FPGAwars/icezum/src-kicad/icezum-alhambra-drawing-1.png

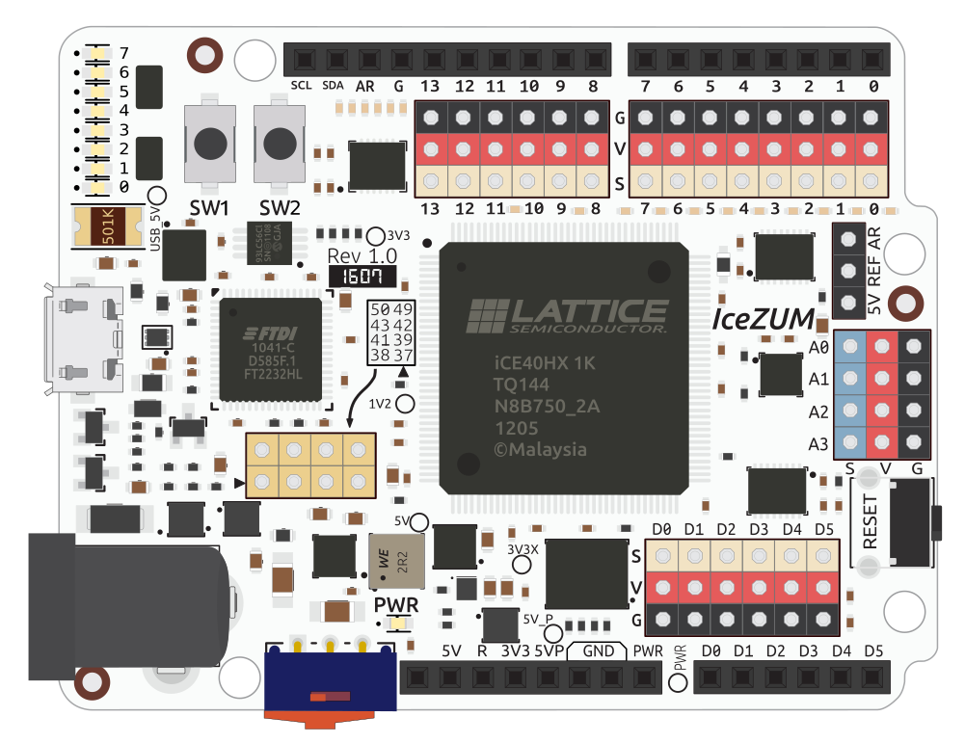
src-kicad/icezum-alhambra-drawing-1.png
