FPGAwars/icezum/src-kicad/images/icezum-block-diagram.png

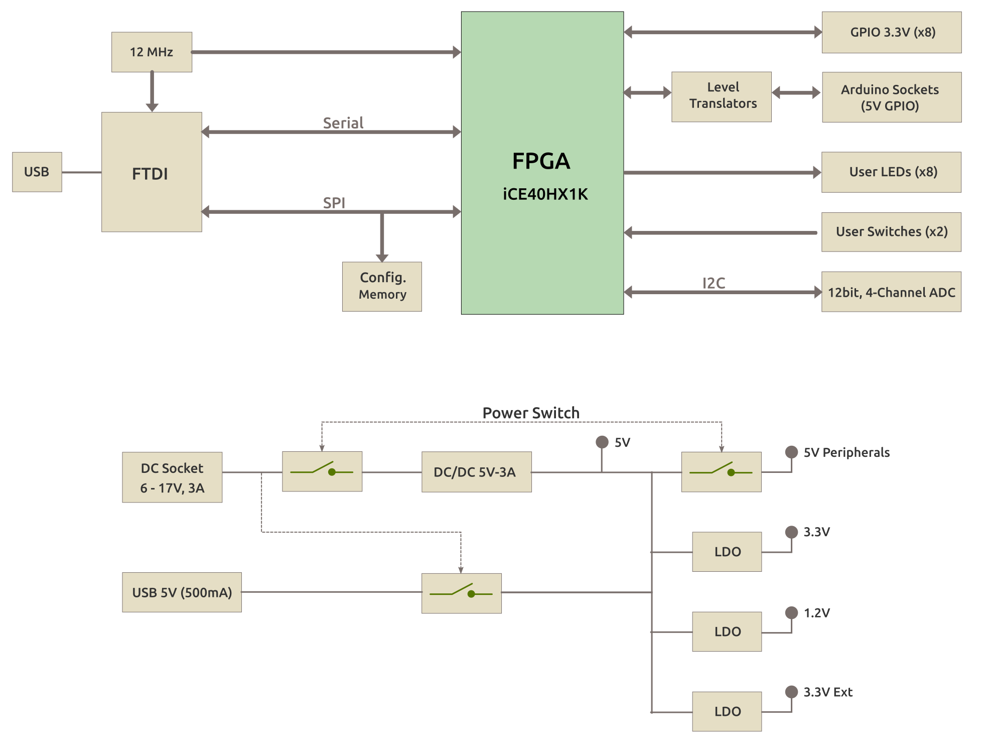
src-kicad/images/icezum-block-diagram.png
