FPGAwars/icezum/wiki/2016-03-04-Mounting-first-prototype/icezum-alhambra-mounting-16.png

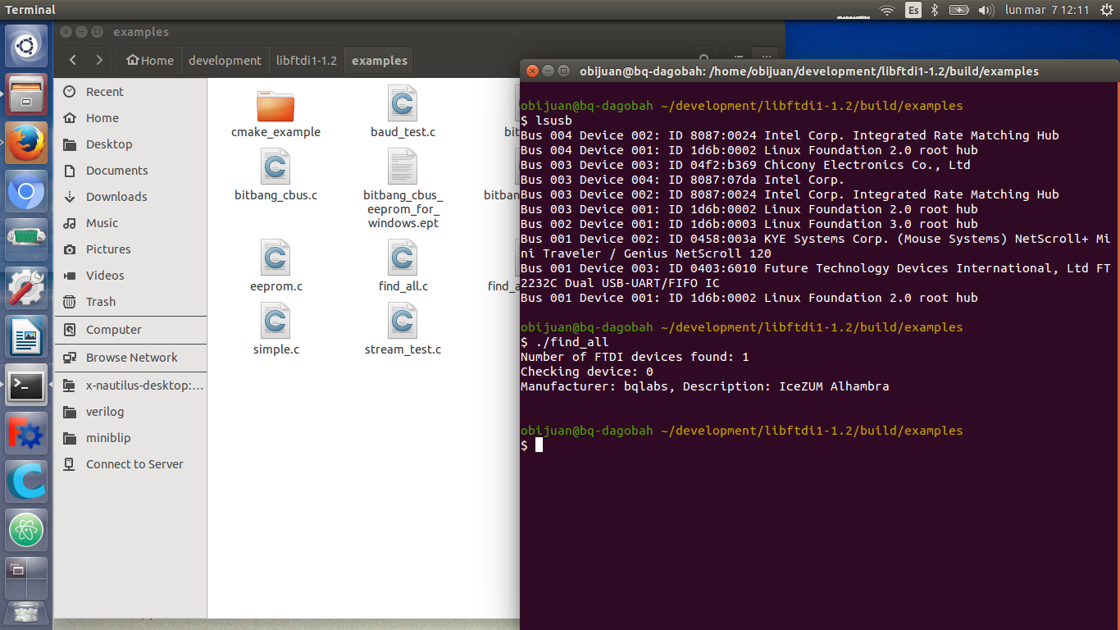
wiki/2016-03-04-Mounting-first-prototype/icezum-alhambra-mounting-16.png
