FPGAwars/icezum/wiki/2016-03-04-Mounting-first-prototype/icezum-alhambra-mounting-18.jpg

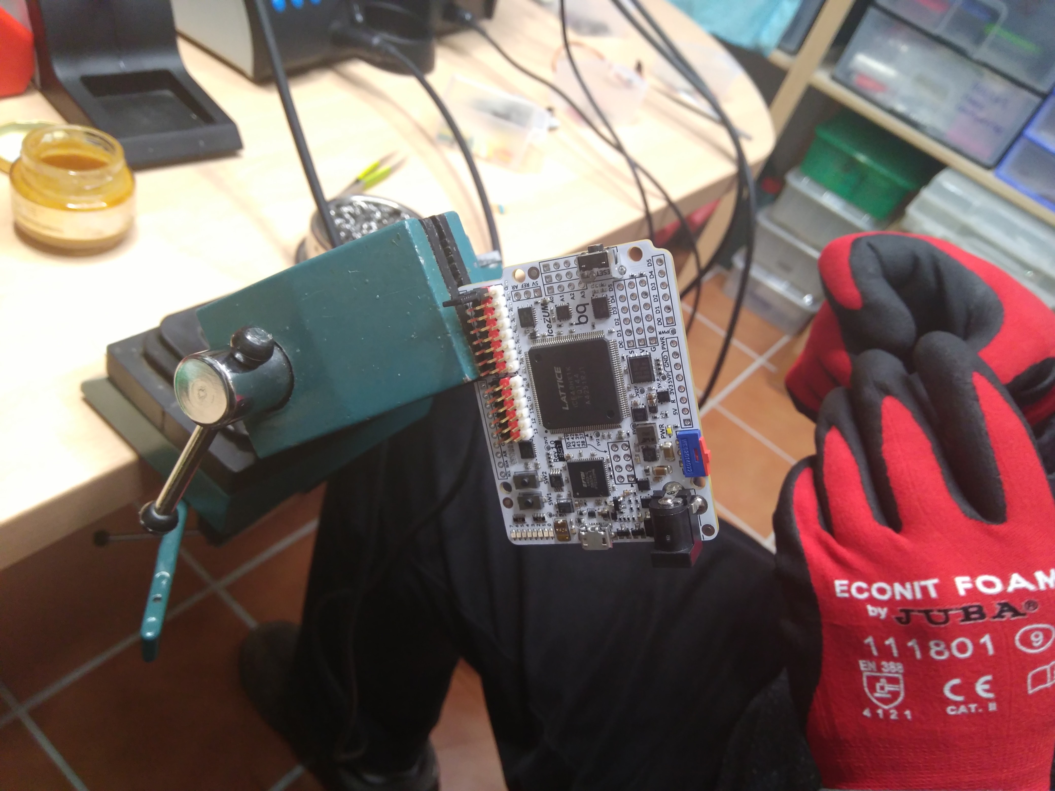
wiki/2016-03-04-Mounting-first-prototype/icezum-alhambra-mounting-18.jpg
