FPGAwars/icezum/wiki/Alhambra_in_the_evening-wikipedia-public-domain.jpg

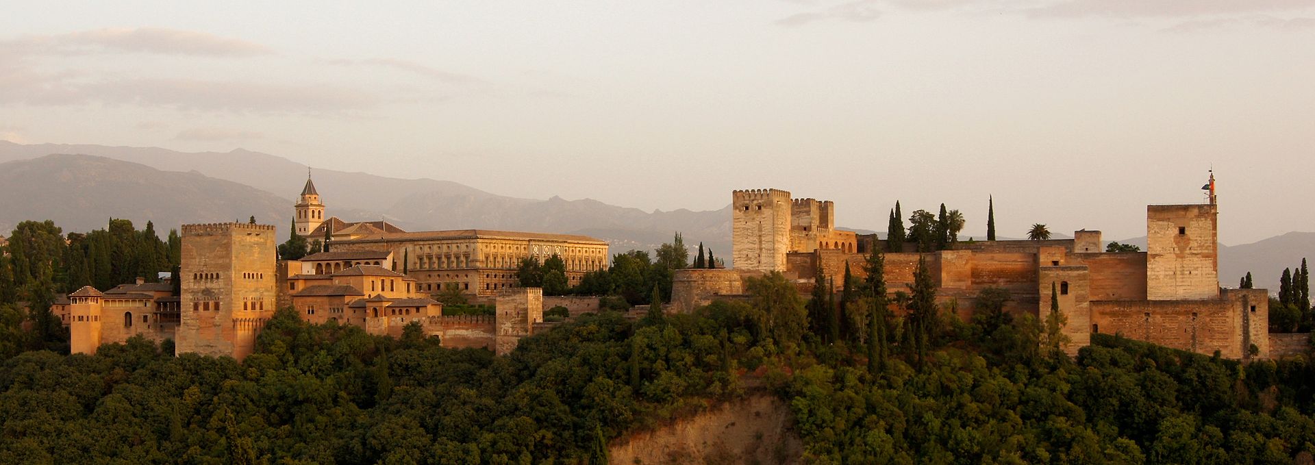
wiki/Alhambra_in_the_evening-wikipedia-public-domain.jpg
