FPGAwars/icezum/wiki/AlhambraFestivales-curdiales.png

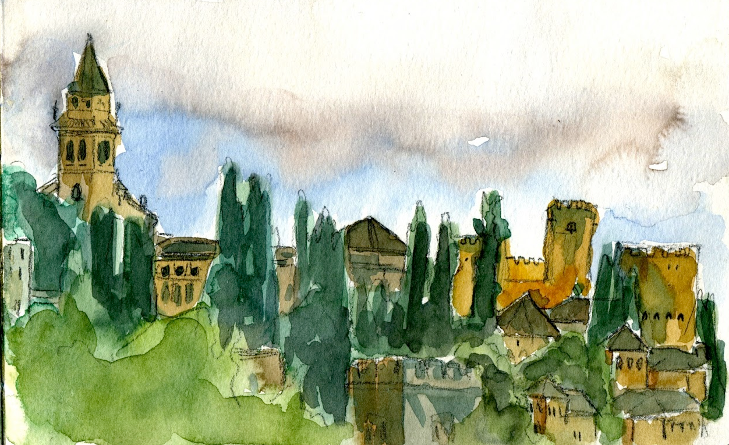
wiki/AlhambraFestivales-curdiales.png
