FPGAwars/icezum/wiki/Icezum-Alhambra-pcb-1.jpg

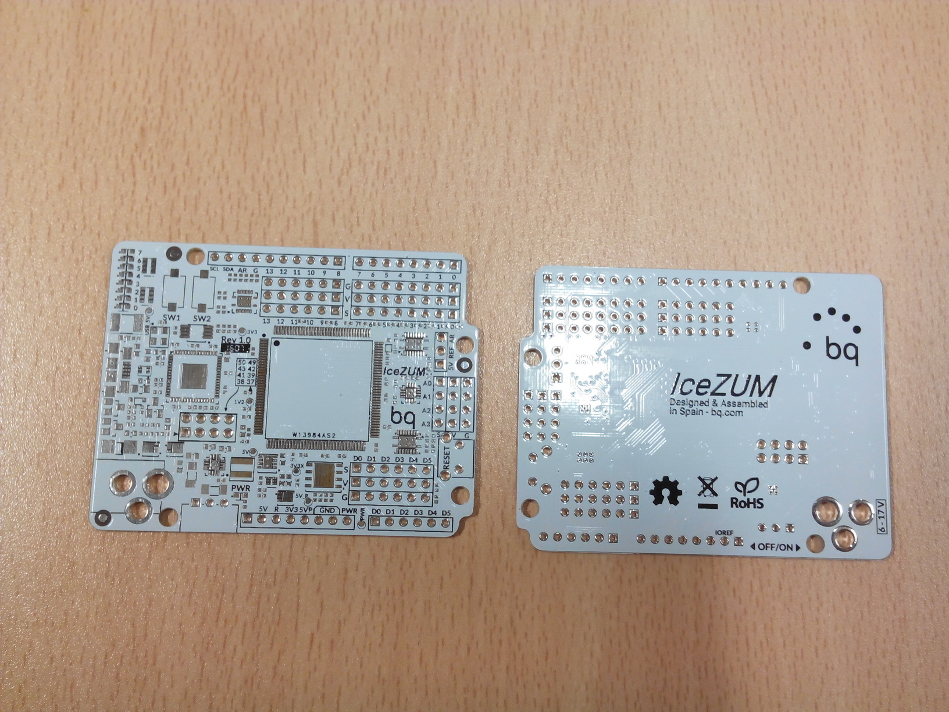
wiki/Icezum-Alhambra-pcb-1.jpg
