FPGAwars/icezum/wiki/icezum-pinout-screenshot-inkscape.png

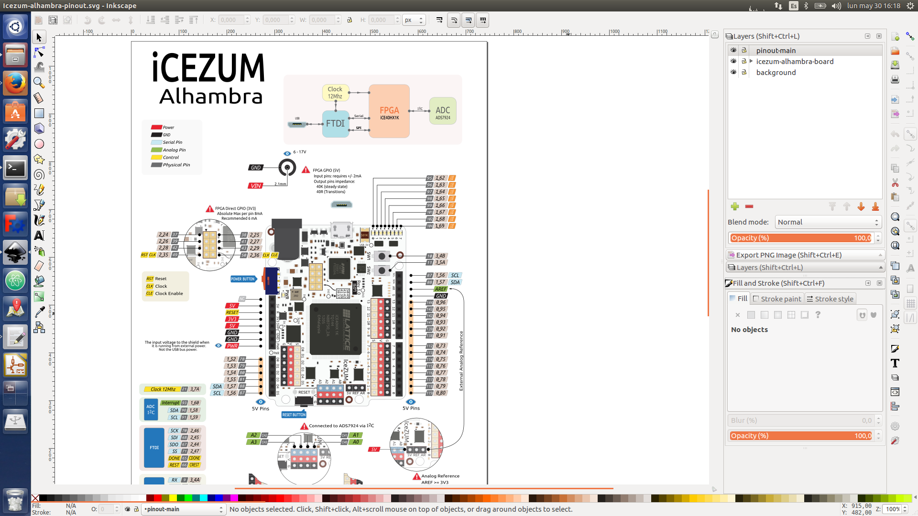
wiki/icezum-pinout-screenshot-inkscape.png
