FPGAwars/icezum/wiki/Icezum-rev1-1607-img1-peq.png

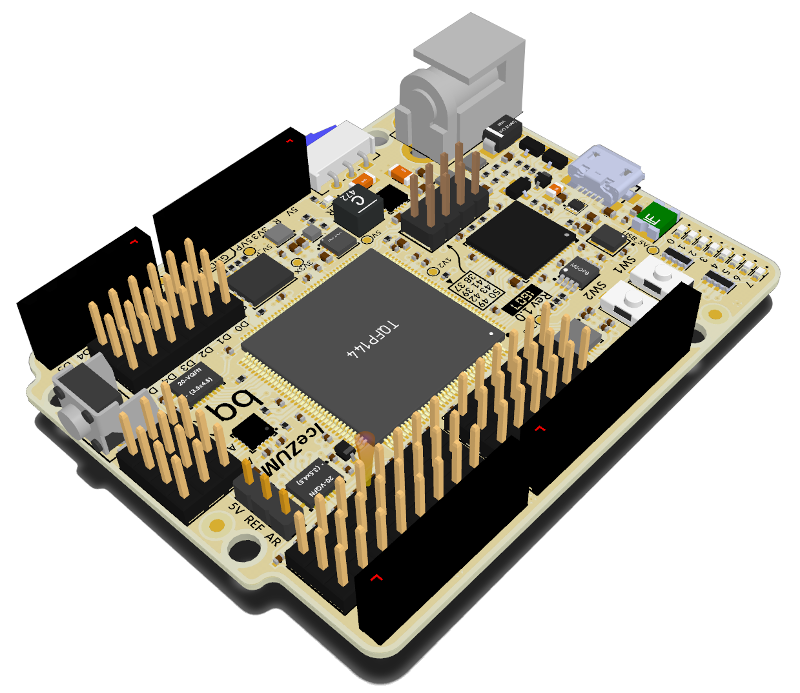
wiki/Icezum-rev1-1607-img1-peq.png
