FPGAwars/icezum/wiki/Icezum-rev1-1607-img2-peq.png

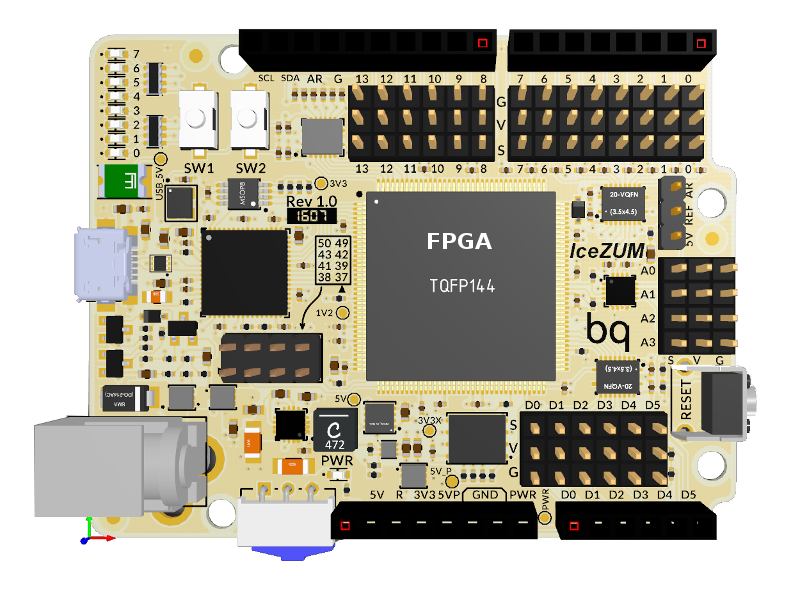
wiki/Icezum-rev1-1607-img2-peq.png
