FPGAwars/icezum/wiki/Icezum-rev1-1607-img3.png

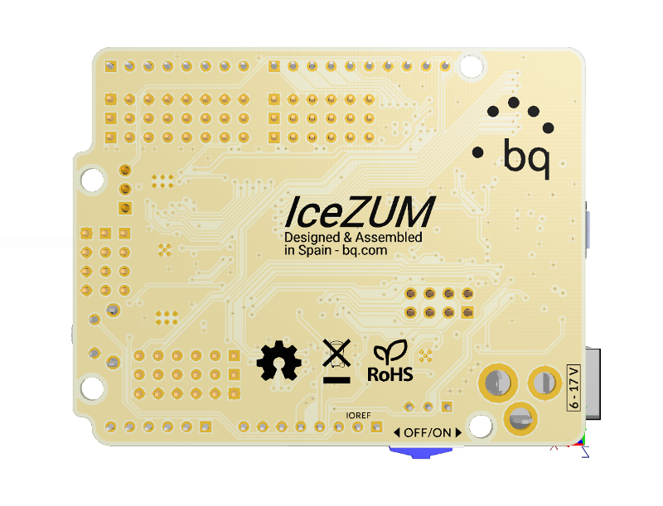
wiki/Icezum-rev1-1607-img3.png
