FPGAwars/icezum/wiki/icezum-rev1-1607-img4.png

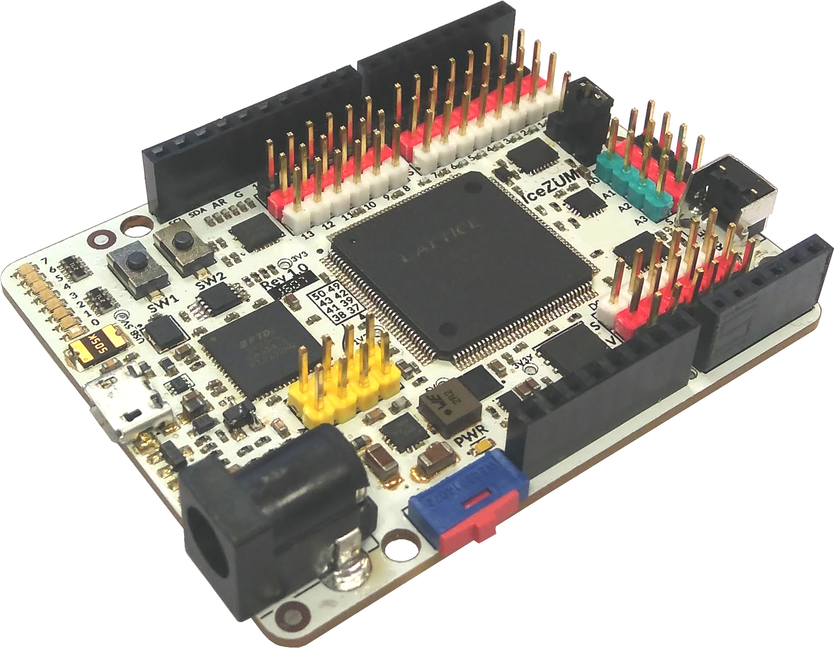
wiki/icezum-rev1-1607-img4.png
