FPGAwars/icezum/wiki/icezum-schematic-kicad-screenshot.png

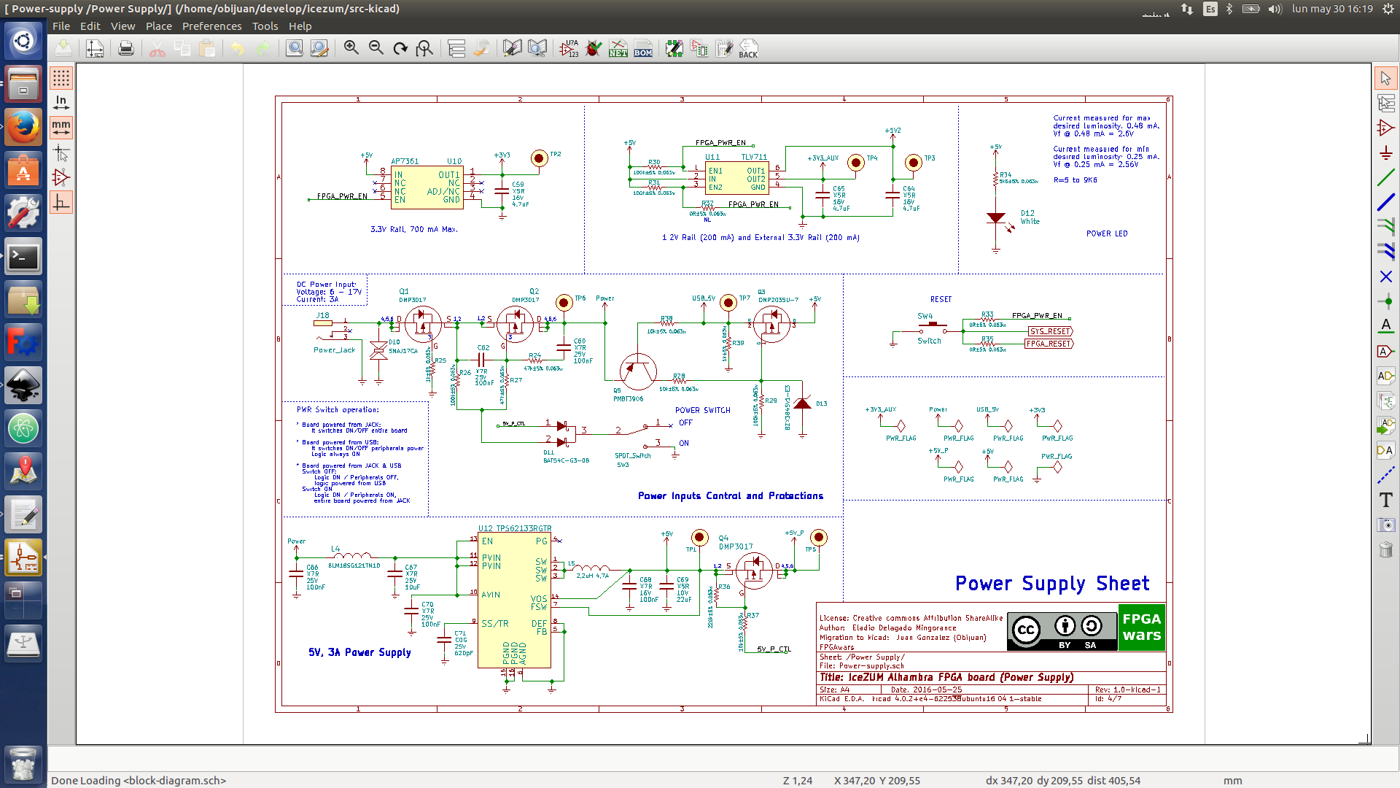
wiki/icezum-schematic-kicad-screenshot.png
