FPGAwars/icezum/wiki/Peripherals/alhambra-led-2.png

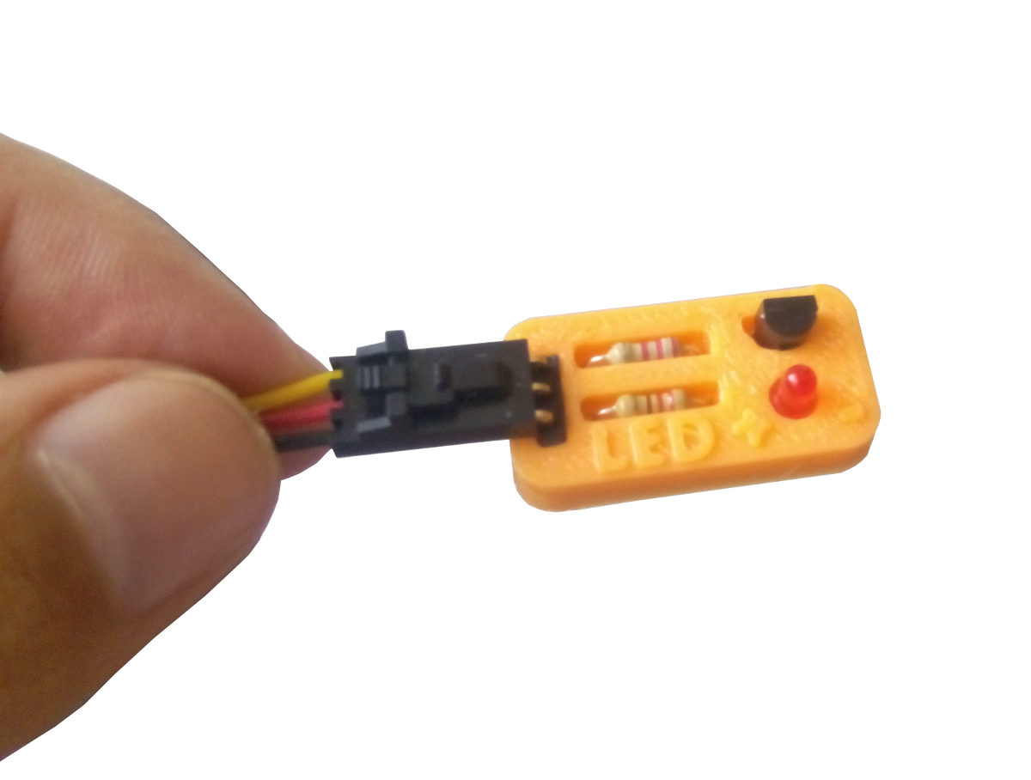
wiki/Peripherals/alhambra-led-2.png
