FPGAwars/icezum/wiki/Peripherals/alhambra-led-3.jpg

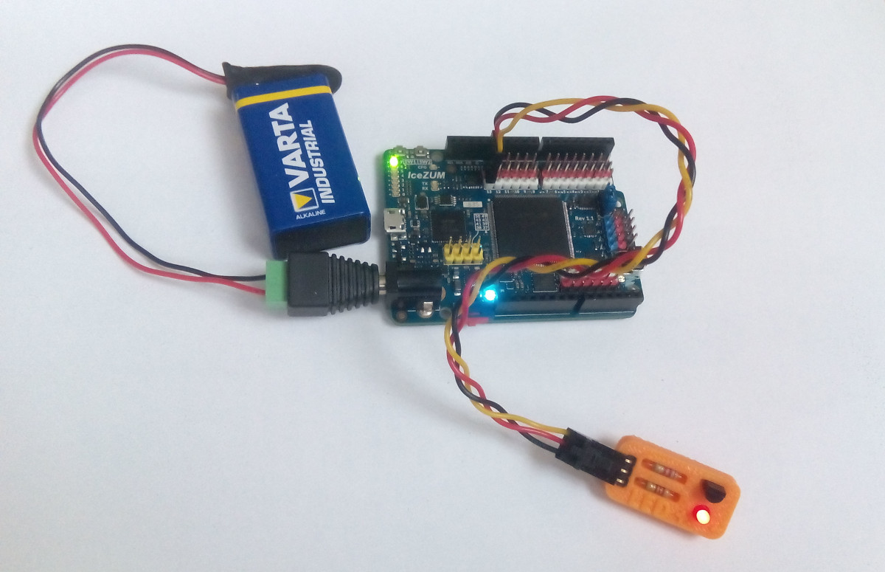
wiki/Peripherals/alhambra-led-3.jpg
