FPGAwars/icezum/wiki/Peripherals/alhambra-led-4.jpg

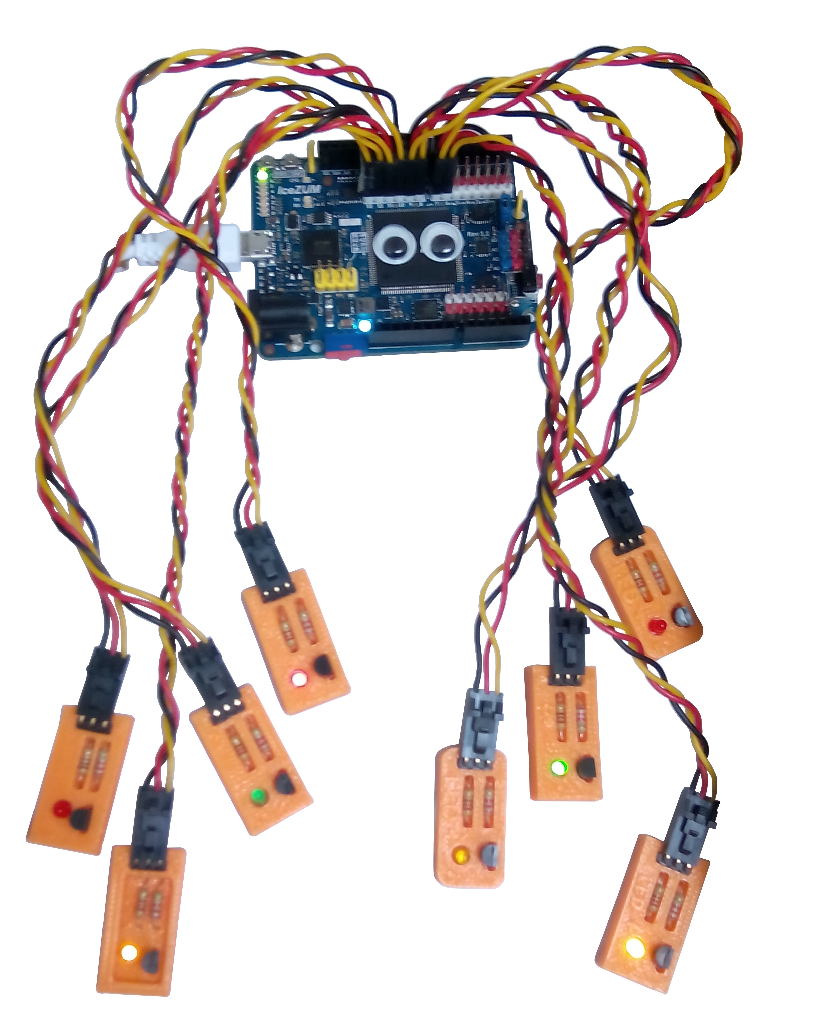
wiki/Peripherals/alhambra-led-4.jpg
