FPGAwars/icezum/wiki/icezum-rev1-1607-components-1.jpg

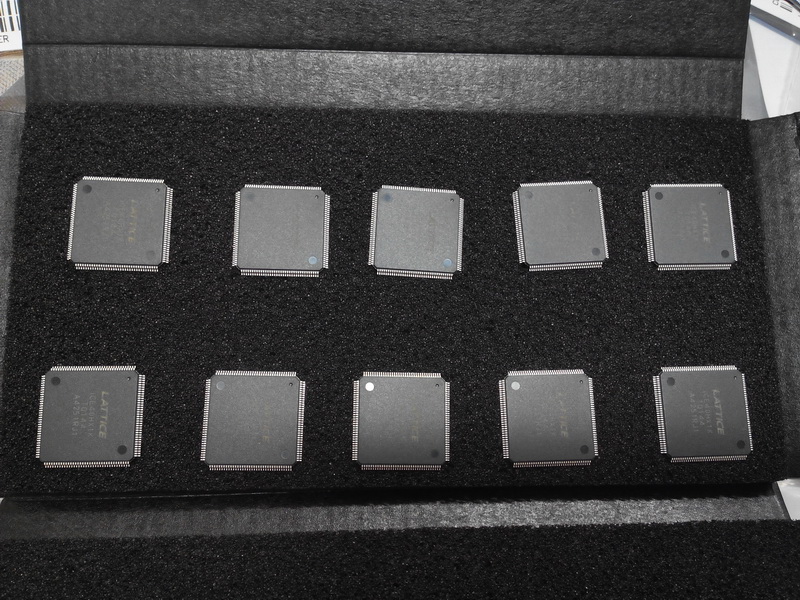
wiki/icezum-rev1-1607-components-1.jpg
