FPGAwars/icezum/wiki/icezum-rev1-1607-components-2.jpg

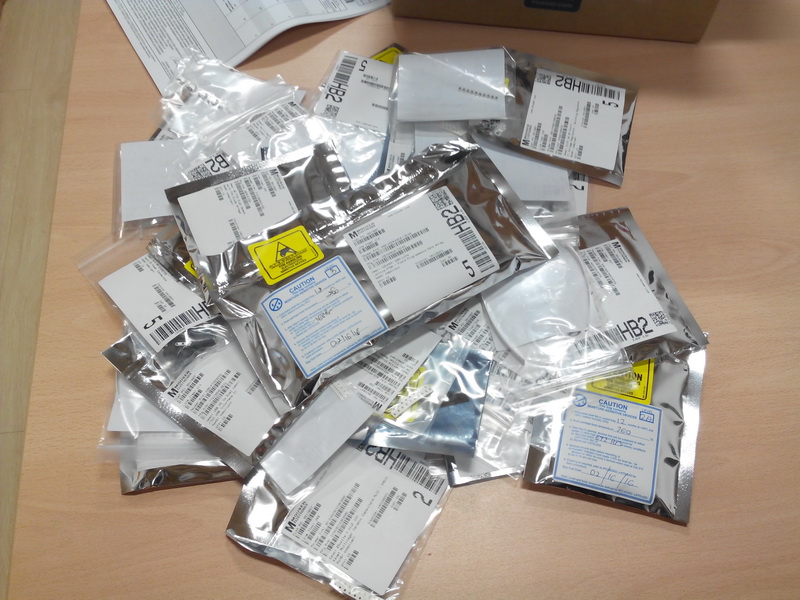
wiki/icezum-rev1-1607-components-2.jpg
