FPGAwars/icezum/wiki/icezum-rev1-1607-components-3.jpg

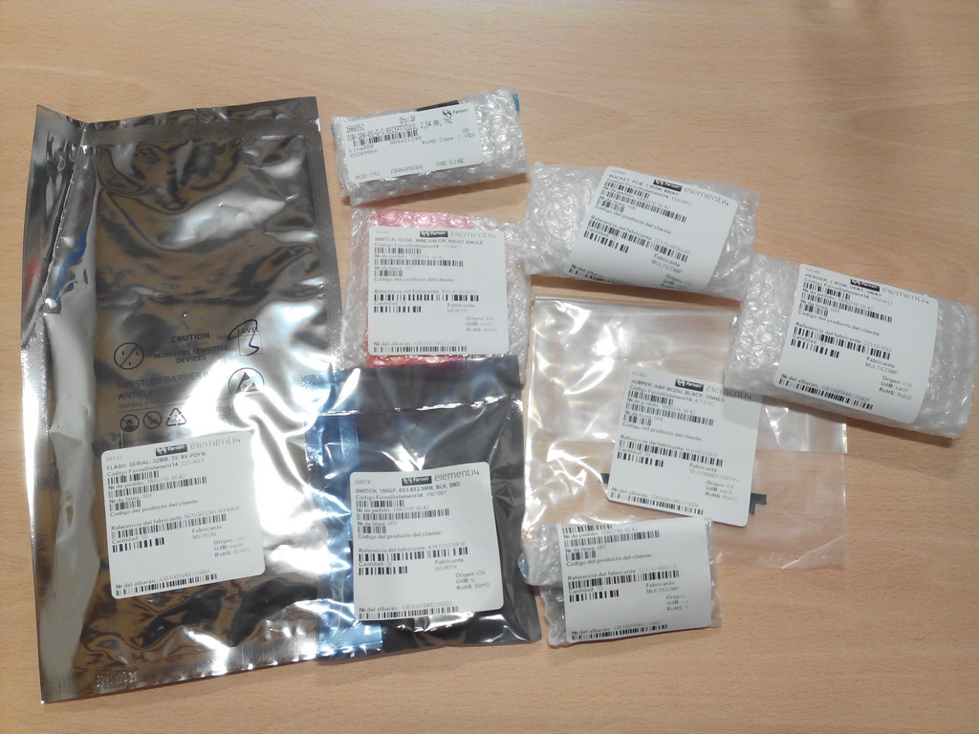
wiki/icezum-rev1-1607-components-3.jpg
