FPGAwars/icezum/wiki/V1.0K/3D-components/1x3-pin-header-2.54mm-3D.png

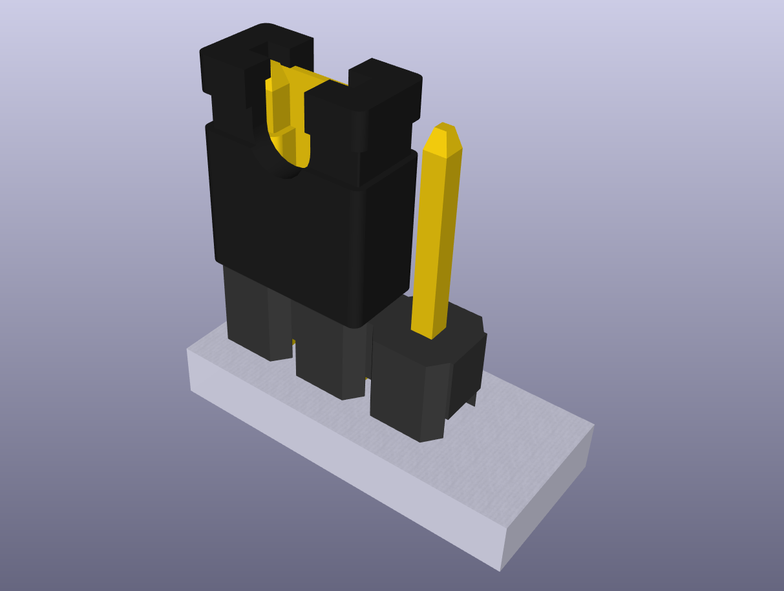
wiki/V1.0K/3D-components/1x3-pin-header-2.54mm-3D.png
