FPGAwars/icezum/wiki/V1.0K/3D-components/1x6-socket-header-2.54-3D.png

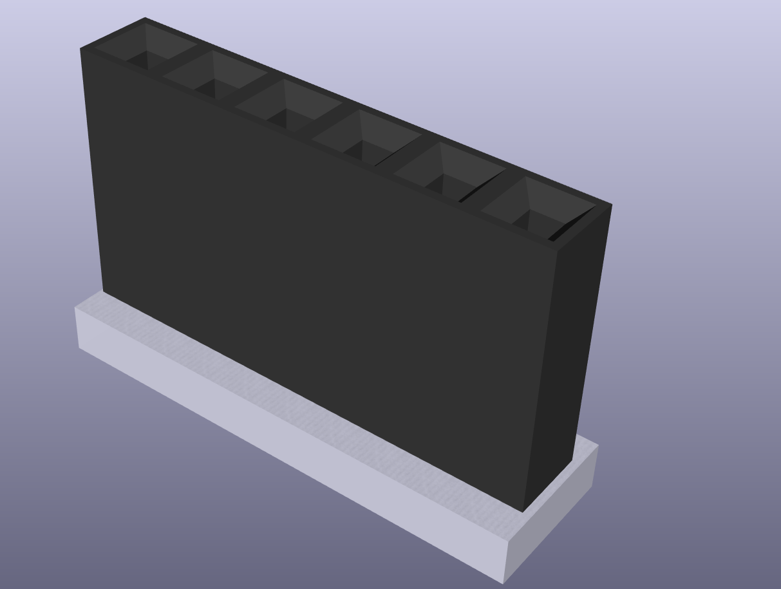
wiki/V1.0K/3D-components/1x6-socket-header-2.54-3D.png
