FPGAwars/icezum/wiki/V1.0K/3D-components/1x10-socket-header-2.54-footprint.png

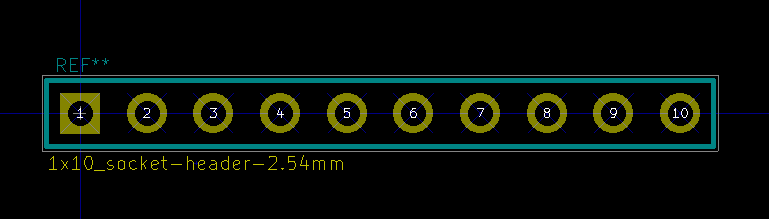
wiki/V1.0K/3D-components/1x10-socket-header-2.54-footprint.png
