FPGAwars/icezum/wiki/V1.0K/3D-components/2x4-pin-header-2.54mm-footprint.png

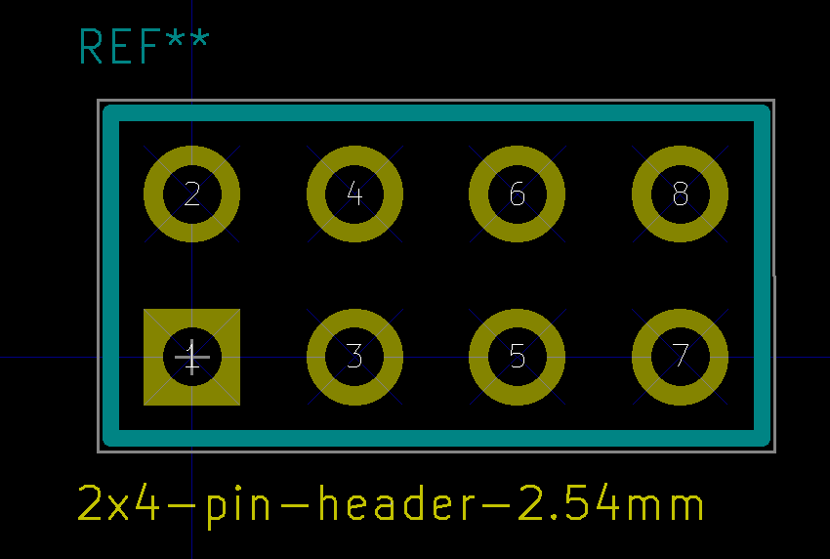
wiki/V1.0K/3D-components/2x4-pin-header-2.54mm-footprint.png
