FPGAwars/icezum/wiki/V1.0K/3D-components/C_0603-footprint.png

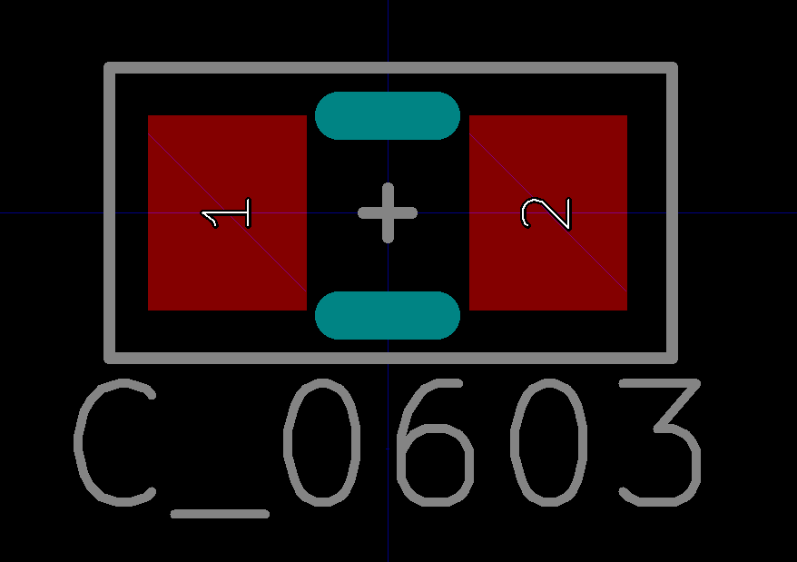
wiki/V1.0K/3D-components/C_0603-footprint.png
