FPGAwars/icezum/wiki/V1.0K/3D-components/C_1206-3D.png

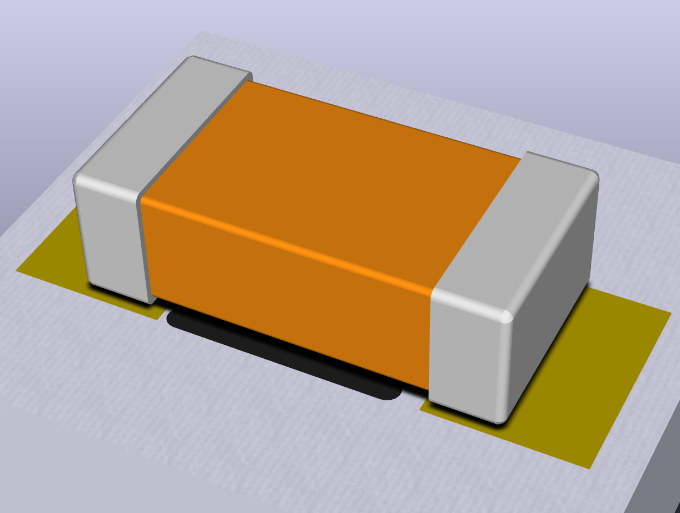
wiki/V1.0K/3D-components/C_1206-3D.png
