FPGAwars/icezum/wiki/V1.0K/3D-components/DFN-8-6X5mm-3D.png

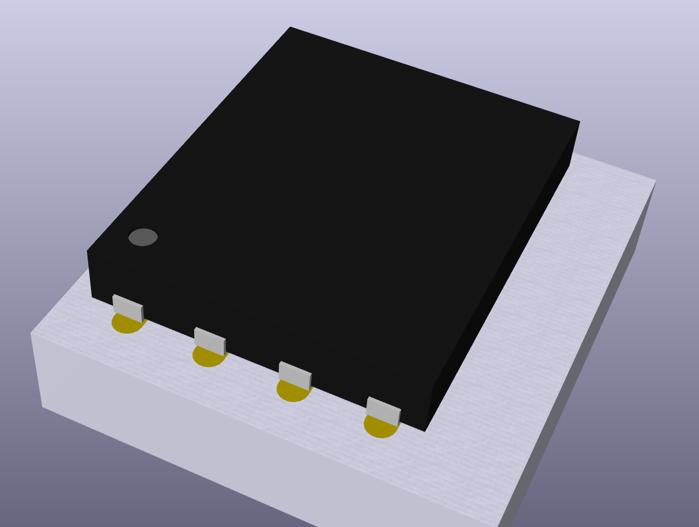
wiki/V1.0K/3D-components/DFN-8-6X5mm-3D.png
