FPGAwars/icezum/wiki/V1.0K/3D-components/DFN-2523-6-3D.png

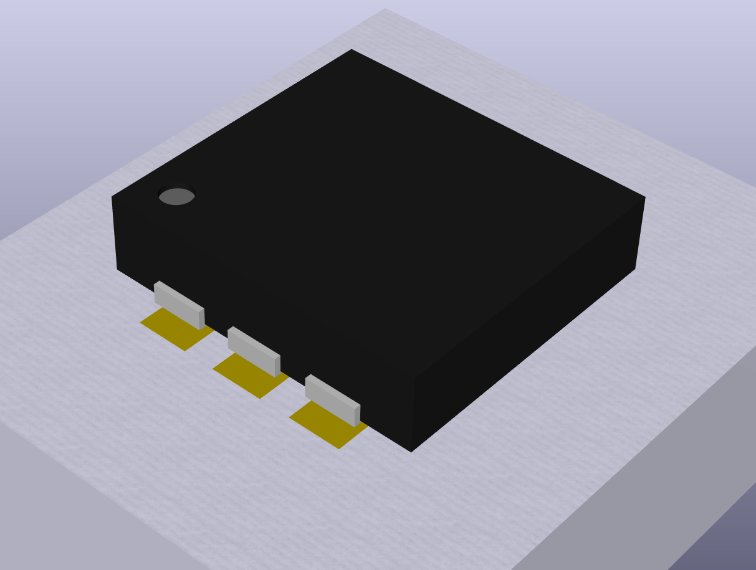
wiki/V1.0K/3D-components/DFN-2523-6-3D.png
