FPGAwars/icezum/wiki/V1.0K/3D-components/DFN-2523-6-footprint.png

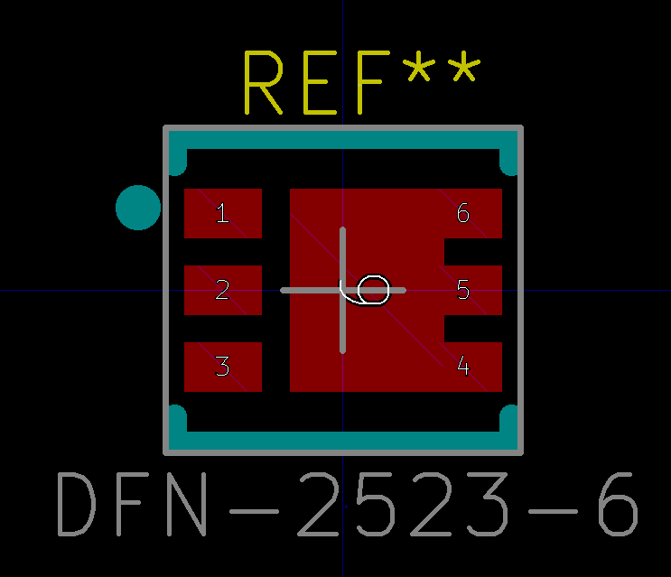
wiki/V1.0K/3D-components/DFN-2523-6-footprint.png
