FPGAwars/icezum/wiki/V1.0K/3D-components/DFN-3030-8-footprint.png

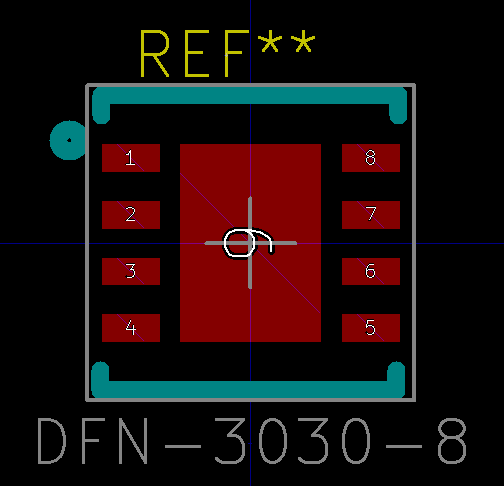
wiki/V1.0K/3D-components/DFN-3030-8-footprint.png
