FPGAwars/icezum/wiki/V1.0K/3D-components/DO-214AC-3D.png

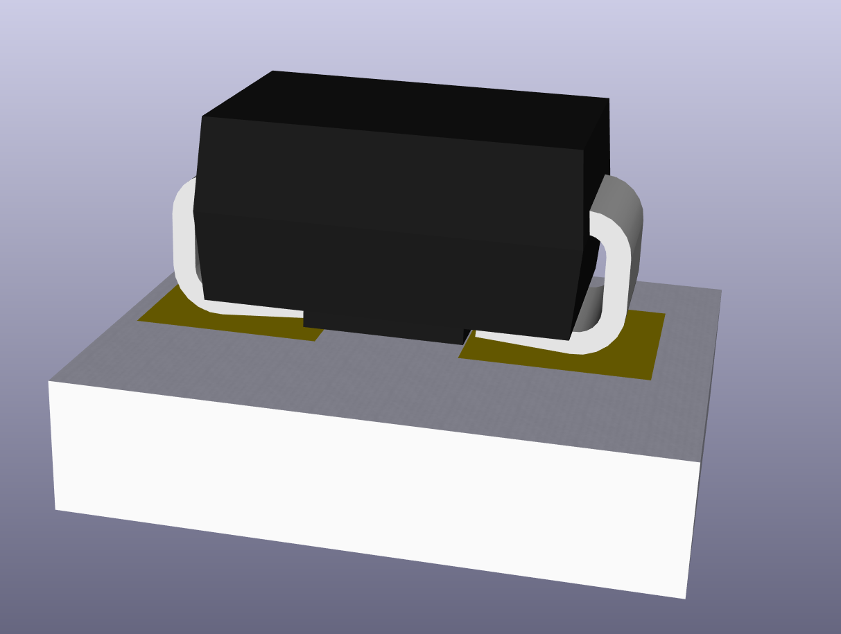
wiki/V1.0K/3D-components/DO-214AC-3D.png
