FPGAwars/icezum/wiki/V1.0K/3D-components/DO-214AC-footprint.png

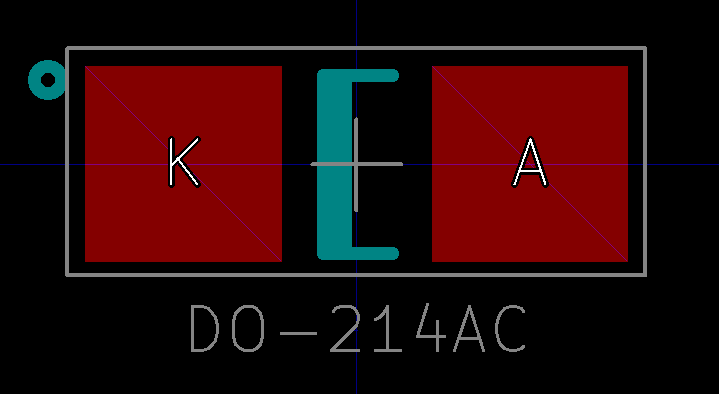
wiki/V1.0K/3D-components/DO-214AC-footprint.png
