FPGAwars/icezum/wiki/V1.0K/3D-components/F_1812-3D.png

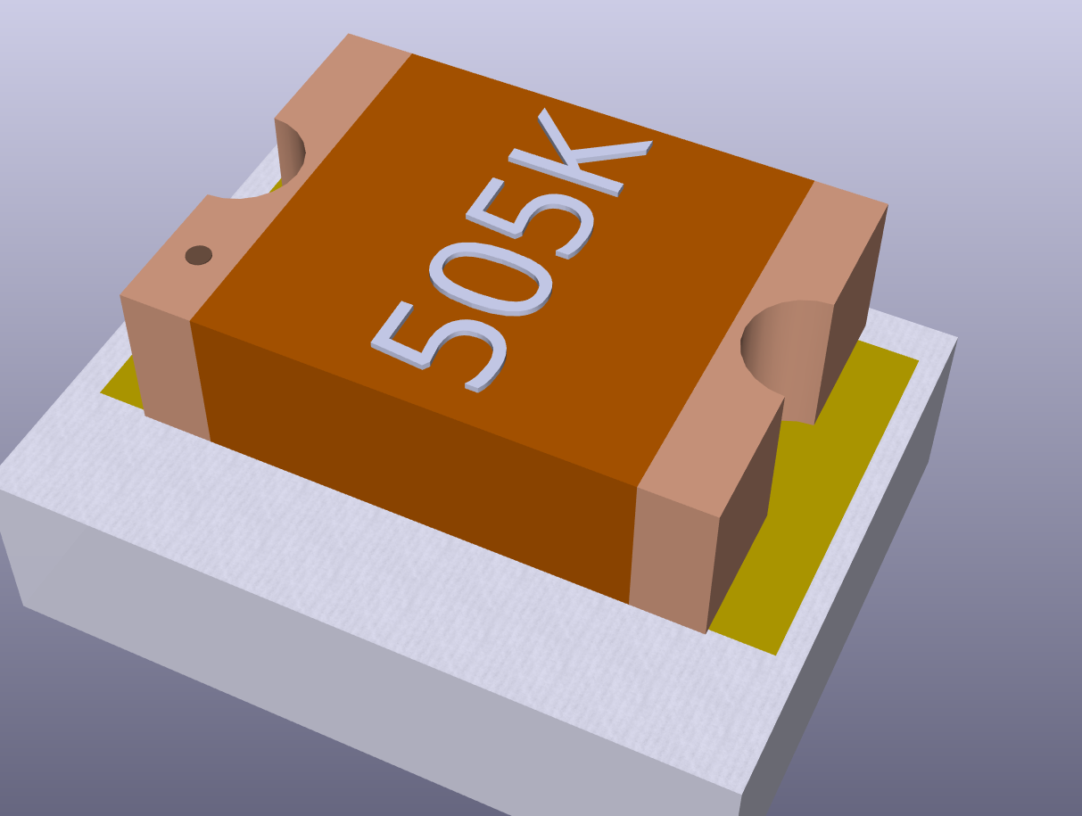
wiki/V1.0K/3D-components/F_1812-3D.png
