FPGAwars/icezum/wiki/V1.0K/3D-components/FTDI-QFN-64-footprint-3D.png

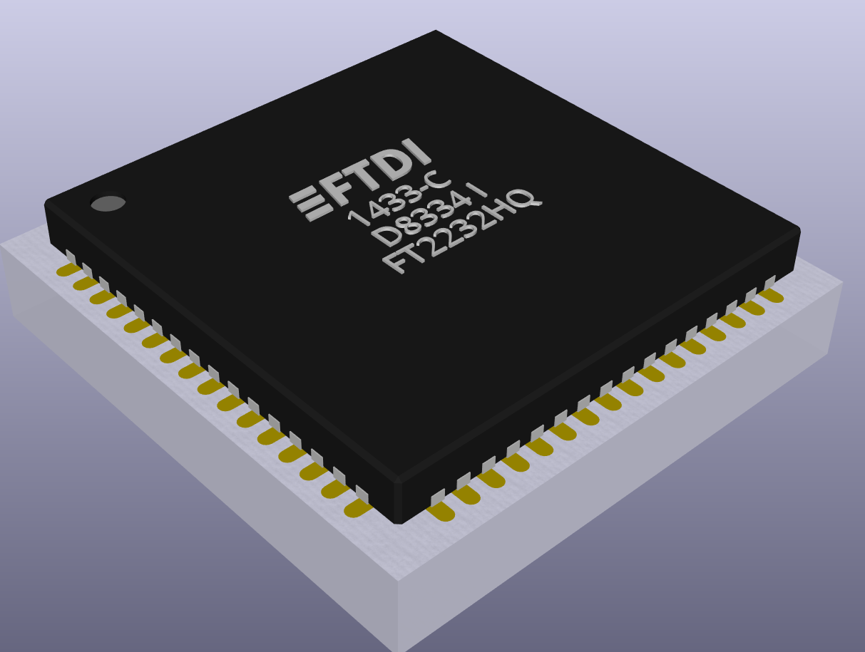
wiki/V1.0K/3D-components/FTDI-QFN-64-footprint-3D.png
