FPGAwars/icezum/wiki/V1.0K/3D-components/FTDI-QFN-64-footprint.png

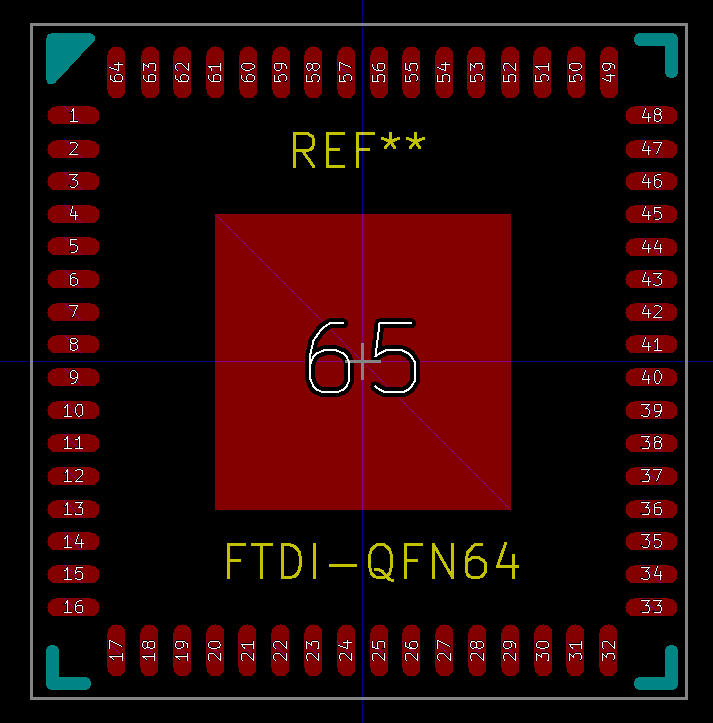
wiki/V1.0K/3D-components/FTDI-QFN-64-footprint.png
