FPGAwars/icezum/wiki/V1.0K/3D-components/jack_2.1-footprint.png

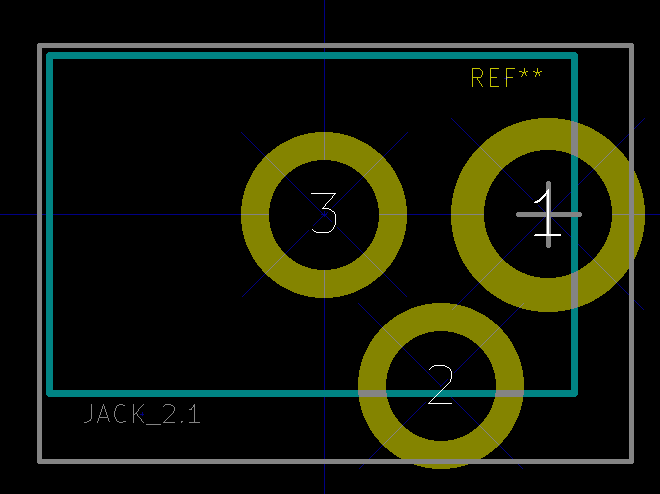
wiki/V1.0K/3D-components/jack_2.1-footprint.png
