FPGAwars/icezum/wiki/V1.0K/3D-components/L_0805-3D.png

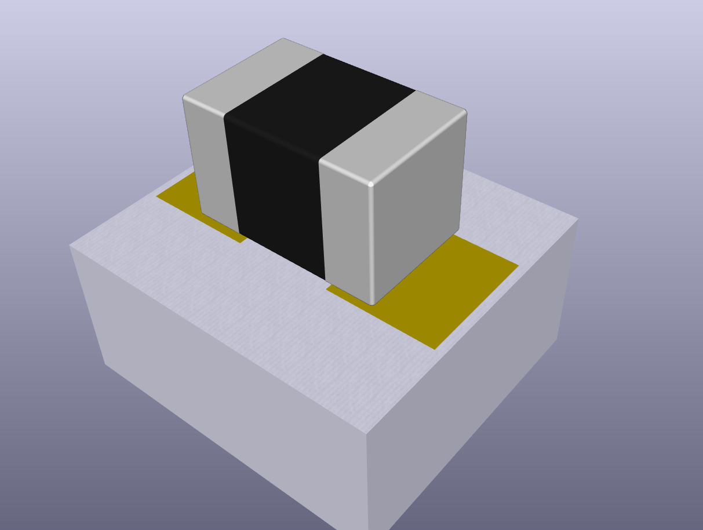
wiki/V1.0K/3D-components/L_0805-3D.png
