FPGAwars/icezum/wiki/V1.0K/3D-components/L_4040-footprint.png

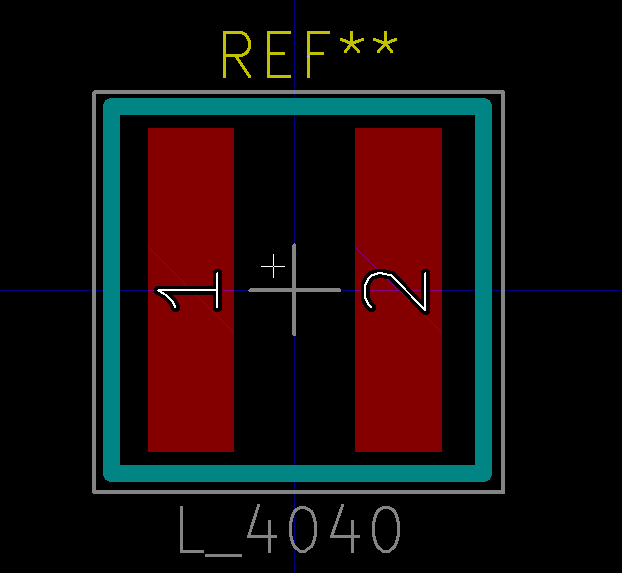
wiki/V1.0K/3D-components/L_4040-footprint.png
