FPGAwars/icezum/wiki/V1.0K/3D-components/LED_0603-footprint.png

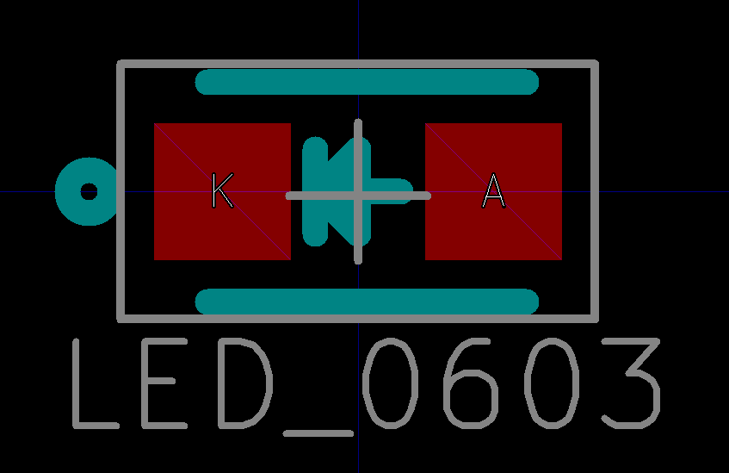
wiki/V1.0K/3D-components/LED_0603-footprint.png
