FPGAwars/icezum/wiki/V1.0K/3D-components/MSOP-8_3x3mm_Pitch0.65mm-3D.png

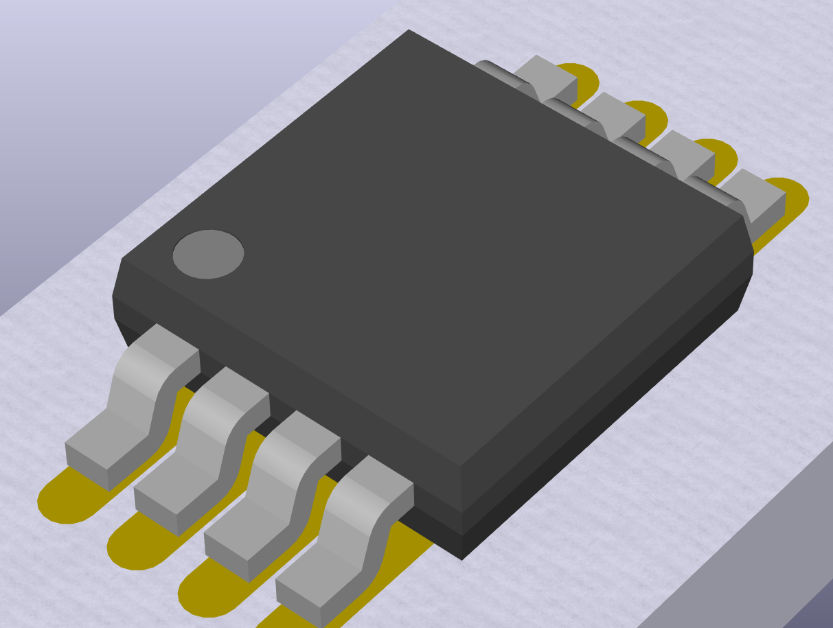
wiki/V1.0K/3D-components/MSOP-8_3x3mm_Pitch0.65mm-3D.png
