FPGAwars/icezum/wiki/V1.0K/3D-components/QFN16-footprint.png

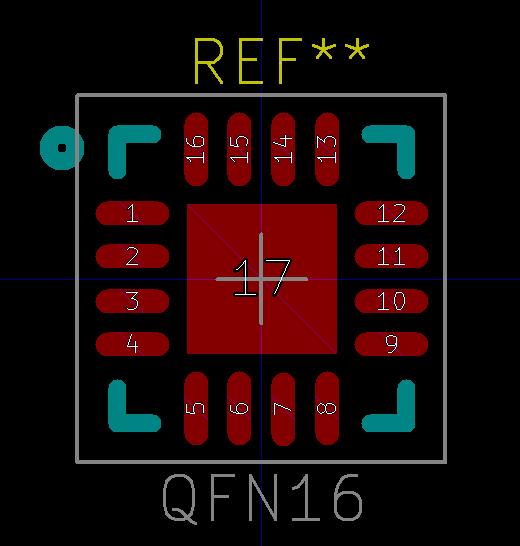
wiki/V1.0K/3D-components/QFN16-footprint.png
