FPGAwars/icezum/wiki/V1.0K/3D-components/R_Array_4x0603-footprint.png

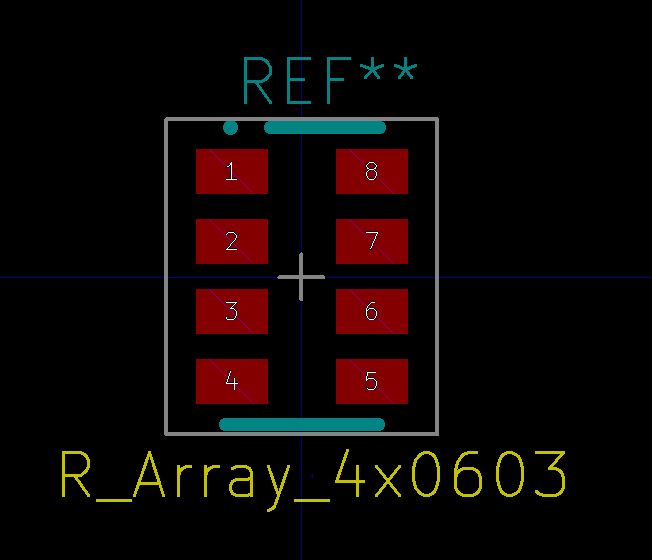
wiki/V1.0K/3D-components/R_Array_4x0603-footprint.png
