FPGAwars/icezum/wiki/V1.0K/3D-components/slide-sw-spdt-right-angle-3D.png

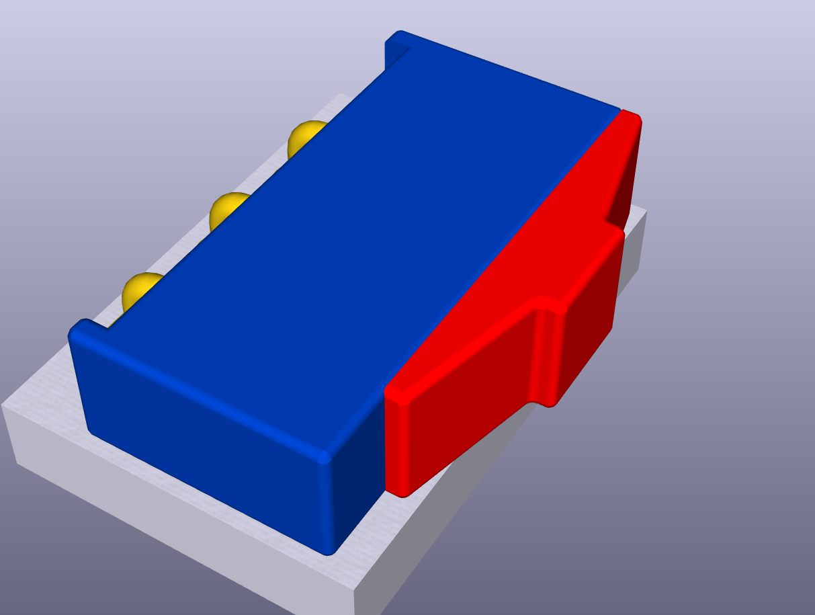
wiki/V1.0K/3D-components/slide-sw-spdt-right-angle-3D.png
