FPGAwars/icezum/wiki/V1.0K/3D-components/SOD-323-footprint.png

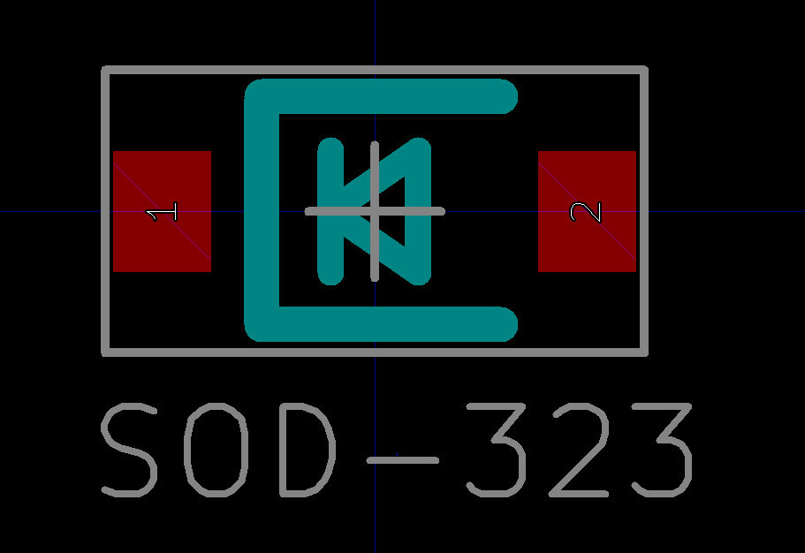
wiki/V1.0K/3D-components/SOD-323-footprint.png
