FPGAwars/icezum/wiki/V1.0K/3D-components/SOT-23-3D.png

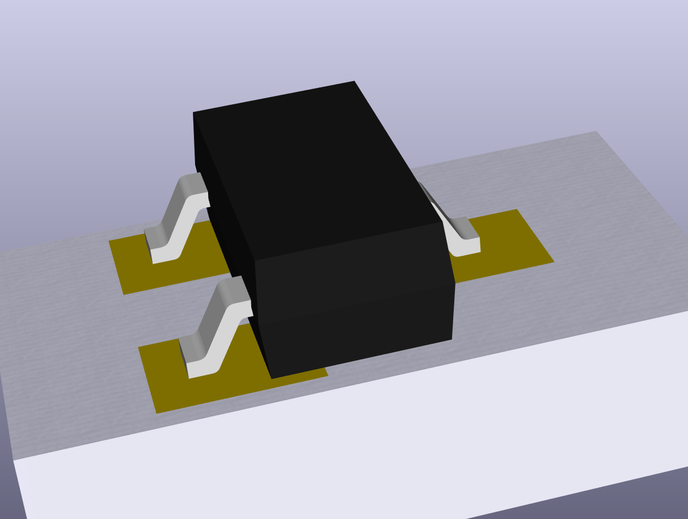
wiki/V1.0K/3D-components/SOT-23-3D.png
