FPGAwars/icezum/wiki/V1.0K/3D-components/SOT-563-footprint.png

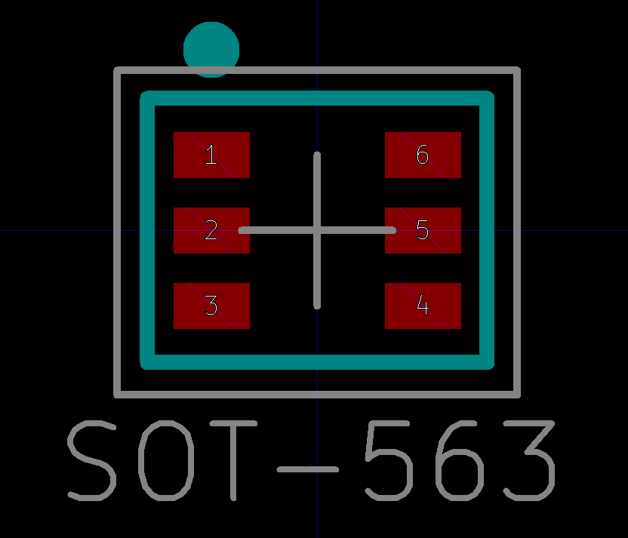
wiki/V1.0K/3D-components/SOT-563-footprint.png
