FPGAwars/icezum/wiki/V1.0K/3D-components/SW_smd_60x3.8-3D.png

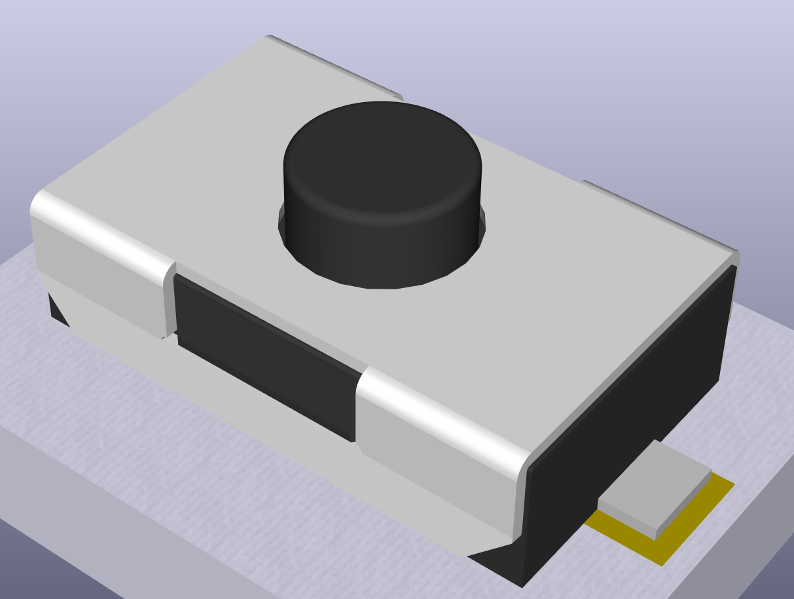
wiki/V1.0K/3D-components/SW_smd_60x3.8-3D.png
