FPGAwars/icezum/wiki/V1.0K/3D-components/SW_vert_tht_7.5x6x6.5-footprint.png

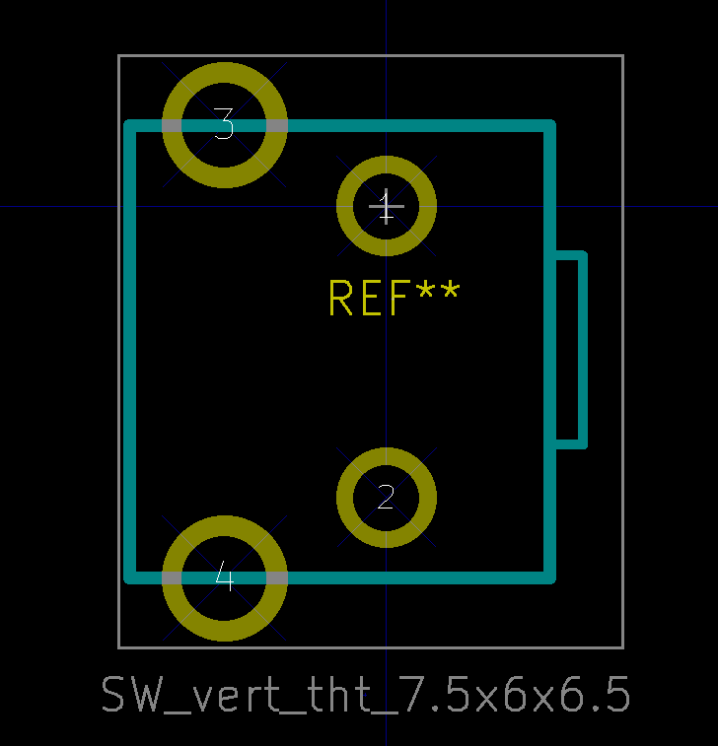
wiki/V1.0K/3D-components/SW_vert_tht_7.5x6x6.5-footprint.png
