FPGAwars/icezum/wiki/V1.0K/3D-components/TQFP-144_IPC-MD-footprint.png

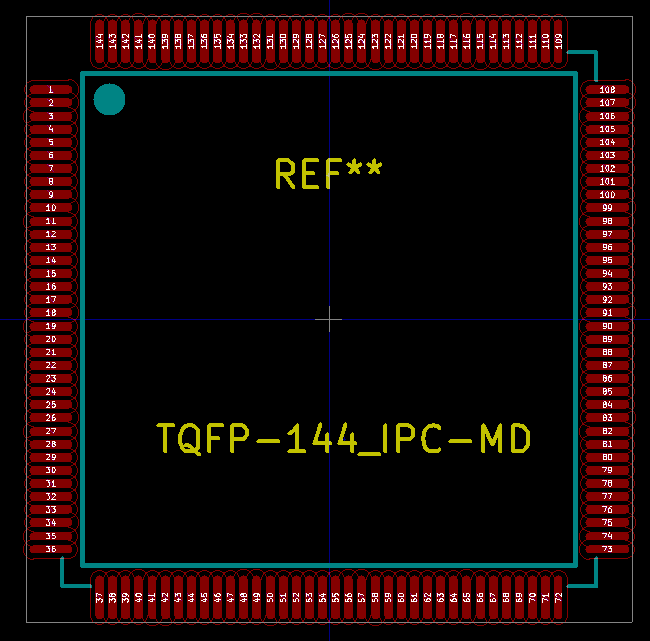
wiki/V1.0K/3D-components/TQFP-144_IPC-MD-footprint.png
