FPGAwars/icezum/wiki/V1.0K/3D-components/USB_micro-B-footprint.png

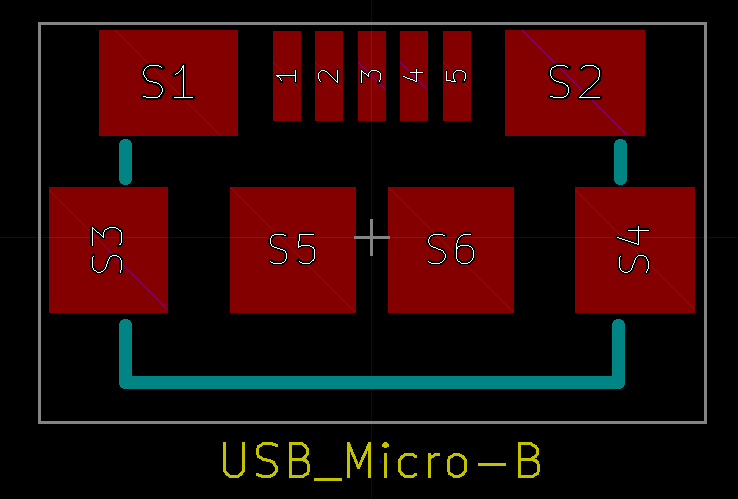
wiki/V1.0K/3D-components/USB_micro-B-footprint.png
