FPGAwars/icezum/wiki/V1.0K/3D-components/VQFN20-3D.png

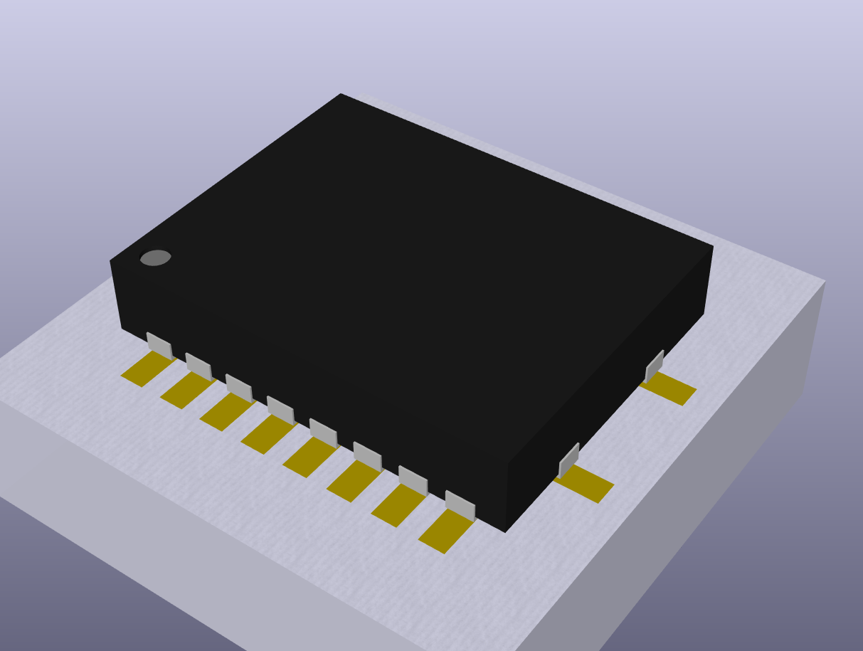
wiki/V1.0K/3D-components/VQFN20-3D.png
