FPGAwars/icezum/wiki/V1.0K/3D-components/VQFN20-footprint.png

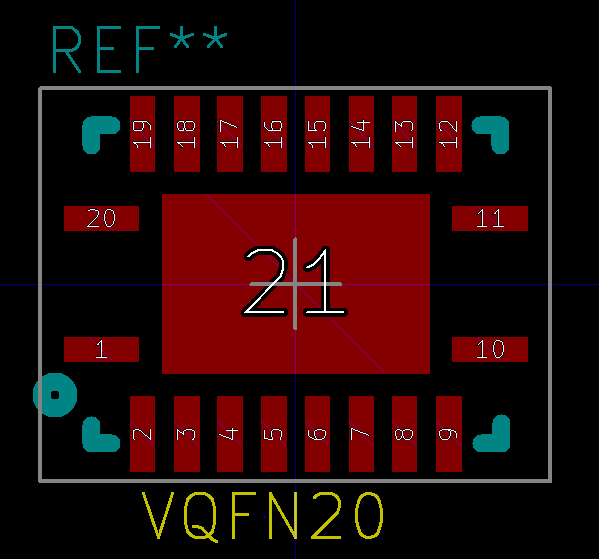
wiki/V1.0K/3D-components/VQFN20-footprint.png
