FPGAwars/icezum/wiki/V1.0K/3D-components/WSON-6-footprint.png

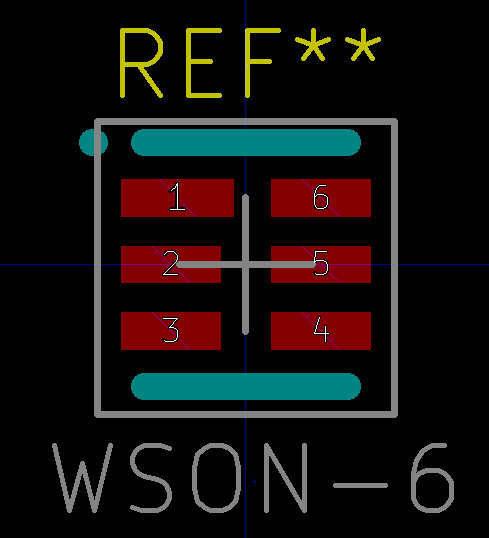
wiki/V1.0K/3D-components/WSON-6-footprint.png
