FPGAwars/icezum/wiki/V1.0K/3D-components/Xtal-3_2x2_5-footprint.png

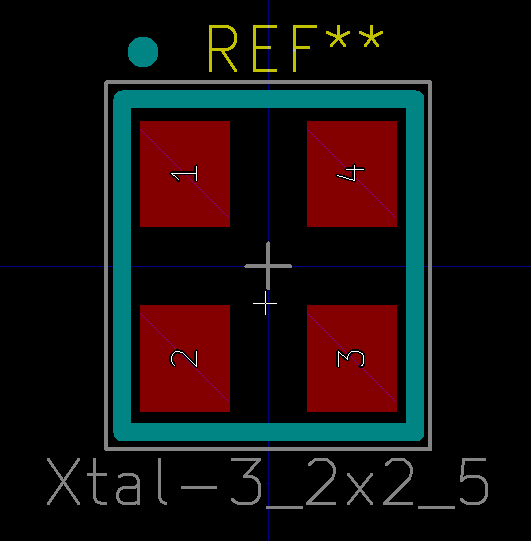
wiki/V1.0K/3D-components/Xtal-3_2x2_5-footprint.png
