FPGAwars/icezum/wiki/2016-03-04-Mounting-first-prototype/Icezum-alhambra-test-2.png

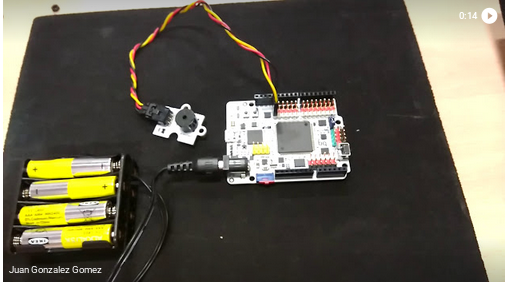
wiki/2016-03-04-Mounting-first-prototype/Icezum-alhambra-test-2.png
