FPGAwars/icezum/wiki/2016-03-04-Mounting-first-prototype/Icezum-alhambra-test-3.jpg

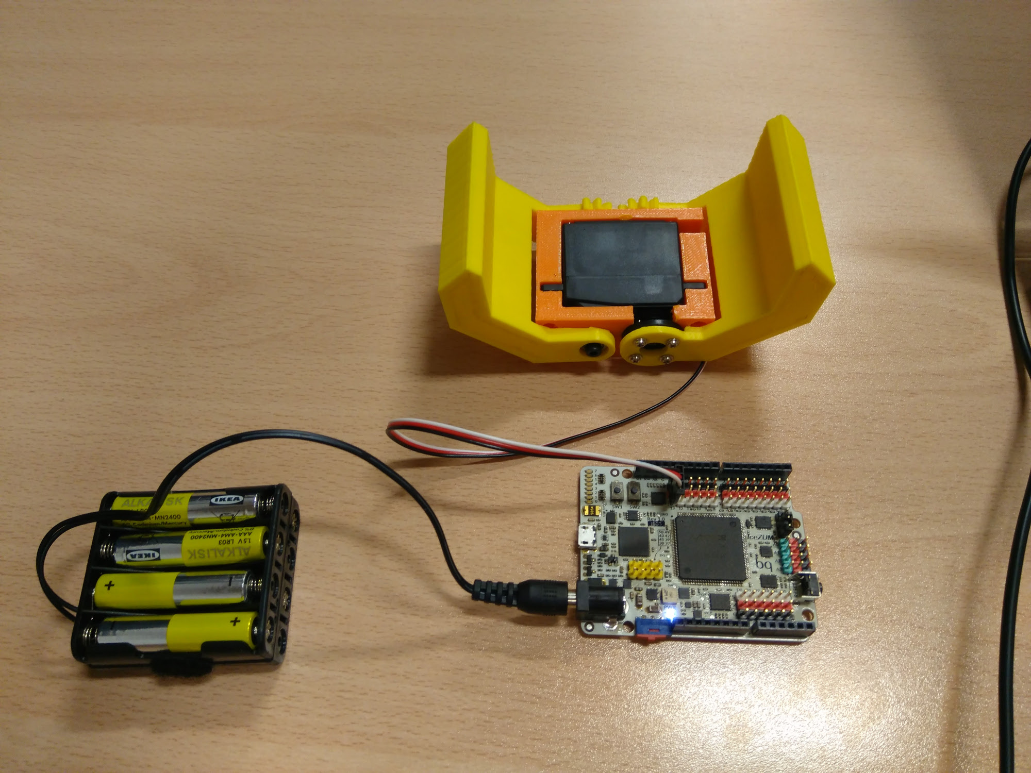
wiki/2016-03-04-Mounting-first-prototype/Icezum-alhambra-test-3.jpg
