FPGAwars/icezum/tests/04-test-echo/echo.v

//----------------------------------------------------------------------------
//-- echo.v: Uart-rx example 2
//-- All the received characters are echoed
//----------------------------------------------------------------------------
//-- (C) BQ. December 2015. Written by Juan Gonzalez (Obijuan)
//-- GPL license
//----------------------------------------------------------------------------
`default_nettype none

`include "baudgen.vh"

//-- Top design
module echo #(
         parameter BAUDRATE = `B115200
)(
         input wire clk,         //-- System clock
         input wire rx,          //-- Serial input
         output wire tx,          //-- Serial output
         output reg [3:0] leds   //-- Red leds
);

//-- Received character signal
wire rcv;

//-- Received data
wire [7:0] data;

//-- Reset signal
reg rstn = 0;

//-- Transmitter ready signal
wire ready;

//-- Initialization
always @(posedge clk)
  rstn <= 1;

//-- Turn on all the red leds
//assign leds = 4'hF;

//-- Show the 4 less significant bits in the leds
always @(posedge clk)
  leds = data[3:0];

//-- Receiver unit instantation
uart_rx #(.BAUDRATE(BAUDRATE))
  RX0 (.clk(clk),
       .rstn(rstn),
       .rx(rx),
       .rcv(rcv),
       .data(data)
      );

//-- Transmitter unit instantation
uart_tx #(.BAUDRATE(BAUDRATE))
  TX0 ( .clk(clk),
         .rstn(rstn),
         .start(rcv),
         .data(data),
         .tx(tx),
         .ready(ready)
       );


endmodule
